coredon17/Octofex/Octo BACK.JPG

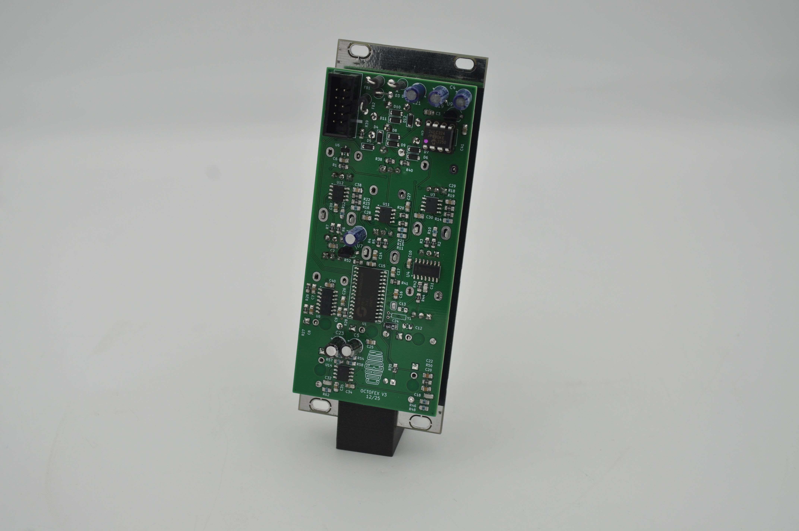
Octo BACK.JPG
